1deam0nster/Vending_materials/Img/photo_2022-11-06_20-43-48.jpg

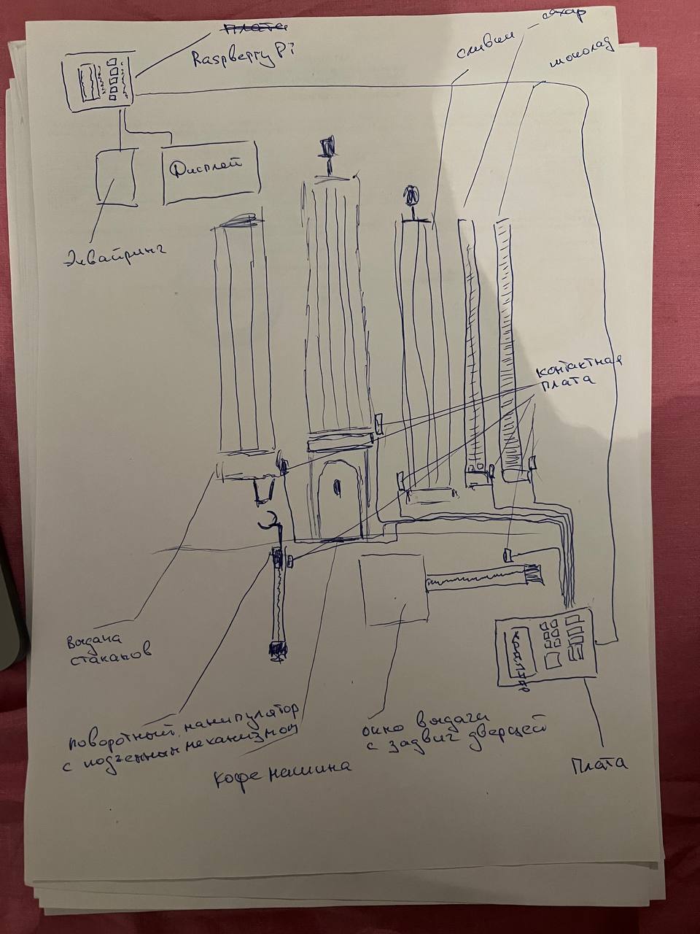
Img/photo_2022-11-06_20-43-48.jpg
