1deam0nster/Vending_materials/Arduino/New firmware arduino/AlmaVending_controll_beta/commands.h

// Открытие и закрытие затвора
void open_mini_servo(){
    //----Открыть затвор
  myservo.attach(turrel_cap_servo_mini);
  for (pos_key = 90; pos_key >= 0; pos_key -= 1) { // goes from 180 degrees to 0 degrees
    myservo.write(pos_key);              // tell servo to go to position in variable 'pos'
    delay(5);                       // waits 15ms for the servo to reach the position
  }
  myservo.detach();
}

void close_mini_servo(){
  //----Закрыть затвор
  myservo.attach(turrel_cap_servo_mini);
  for (pos_key = 0; pos_key <= 90; pos_key += 1) { // goes from 0 degrees to 180 degrees
    // in steps of 1 degree
    myservo.write(pos_key);              // tell servo to go to position in variable 'pos'
    delay(15);                       // waits 15ms for the servo to reach the position
  }
  myservo.detach();
}


//-----------------Проверка-------------
void shake_cap_turrel(){
  //возврат в обычное положение для прокручивания турели
  for (big_pos_cap = 500; big_pos_cap <= 1800; big_pos_cap += 1) {
    cap_drop.writeMicroseconds(big_pos_cap);              
    delay(2);                       
  }
  turrelCurrentPosition = turrel.currentPosition();
  turrel_rotate(turrelCurrentPosition + 50, 1000, 1000);
  delay(100);
  turrel_rotate(turrelCurrentPosition - 50, 1000, 1000);
  delay(100);
  turrel_rotate(turrelCurrentPosition + 50, 1000, 1000);
  delay(100);
  turrel_rotate(turrelCurrentPosition - 50, 1000, 1000);
  for (big_pos_cap = 1800; big_pos_cap >= 1200; big_pos_cap -= 1) {
    cap_drop.writeMicroseconds(big_pos_cap);              
    delay(10);                       
  }
  cap_check();
}

void good_state_drop(){
  Serial.println("начало сброса"); 
  //сброс капсулы
  for (big_pos_cap = 1200; big_pos_cap >= 500; big_pos_cap -= 1) {
    cap_drop.writeMicroseconds(big_pos_cap);              
    delay(5);                       
  }
  
  //возврат в обычное положение
  for (big_pos_cap = 500; big_pos_cap <= 2500; big_pos_cap += 1) {
    cap_drop.writeMicroseconds(big_pos_cap);              
    delay(2);                       
  }
  
  close_mini_servo();

  //положение для прокручивания турели и загрузки капсулы
  for (big_pos_cap = 2500; big_pos_cap >= 1800; big_pos_cap -= 1) {
    cap_drop.writeMicroseconds(big_pos_cap);              
    delay(5);                       
  }
}

void false_state_drop(){
  //возврат в обычное положение
  for (big_pos_cap = 1200; big_pos_cap <= 2500; big_pos_cap += 1) {
    cap_drop.writeMicroseconds(big_pos_cap);              
    delay(2);                       
  }
  
  close_mini_servo();

  //положение для прокручивания турели и загрузки капсулы
  for (big_pos_cap = 2500; big_pos_cap >= 1800; big_pos_cap -= 1) {
    cap_drop.writeMicroseconds(big_pos_cap);              
    delay(5);                       
  }
  Serial.println("Очередь не выпадает");
}

void cap_check(){
  bool check = digitalRead(ir_cap);
  bool check_state;
  DEBUG(cap_check_value);
  cap_check_value += 1;
  switch (check) {
    case 0: 
      check_state = 0;
      Serial.println("Cap OK"); 
      good_state_drop();
      break; 
    case 1: 
      check_state = 1; 
      switch (cap_check_value) {
        case 0: Serial.println("Cap FALSE"); shake_cap_turrel(); break;
        case 1: Serial.println("Cap FALSE"); shake_cap_turrel(); break;
        case 2: Serial.println("Cap FALSE"); shake_cap_turrel(); break;
        case 3: Serial.println("ALL FALSE"); cap_check_value = 0; false_state_drop(); break;
      }
  }
}

// -----------------Command C0-------------
void drop_cap()
{
  //приподнимаем капсулы 
  for (big_pos_cap = 1800; big_pos_cap <= 2500; big_pos_cap += 1) {
    cap_drop.writeMicroseconds(big_pos_cap);              
    delay(5);                       
  }

  //открывваем мини серву
  open_mini_servo();
  
  //положение для загрузки капсулы
  for (big_pos_cap = 2500; big_pos_cap >= 1800; big_pos_cap -= 1) {
    cap_drop.writeMicroseconds(big_pos_cap);              
    delay(5);                       
  }

  Serial.println("забираем капсулу и идем в позицию проверки"); 
  //забираем капсулу и идем в позицию проверки
  for (big_pos_cap = 1800; big_pos_cap >= 1200; big_pos_cap -= 1) {
    cap_drop.writeMicroseconds(big_pos_cap);              
    delay(10);                       
  }

  //код для проверки капсулы
  Serial.println("код для проверки капсулы"); 
  cap_check();
}




// -----------------Command C1-------------
void check_machine() {
  pinMode(cofe_machine_check_button_pin, OUTPUT);
  digitalWrite(cofe_machine_check_button_pin, LOW);
  delay(2000);
  digitalWrite(cofe_machine_check_button_pin, HIGH);
  Serial.println(F("Check machine true"));
  void display_print();
}

// -----------------Command C2-------------
void start_coffe() {
  pinMode(coffe_machine_start_pin, OUTPUT);
  digitalWrite(coffe_machine_start_pin, LOW);
  //delay(1.5 * 60 * 1000); //sleep some minute
  delay(10000);
  do {
    // 1 - можно загружать
    // 0 - наливает кофе
    machine_sensor = digitalRead(cofe_machine_ir);
    Serial.println("Сенсор == 1");
    digitalWrite(coffe_machine_start_pin, LOW);
  } while (machine_sensor == 1);
  delay(7000);
  digitalWrite(coffe_machine_start_pin, HIGH);
  Serial.println(F("End coffe works"));
}
// -----------------Command C4-------------
void choco_check() {
  if (digitalRead(choco_ir_control) == 0) {
    Serial.println("Choco OK");
  } else {
    Serial.println("Choco False");
  }
}

// -----------------Command C5-------------
void sugar_check() {
  if (digitalRead(sugar_ir_control) == 0) {
    Serial.println("Sugar OK");
  } else {
    Serial.println("Sugar False");
  } 
}

// -----------------Command P0-------------
void sugar_command() {
  sugar.attach(sugar_servo);
  delay(1000);
  sugar.write(80);
  delay(1000);
  sugar.write(180);
  delay(1000);
  sugar.write(80);
  sugar.detach();
}
// -----------------Command P1-------------
void chocolate_command() {
  chocolate.attach(choco_servo);
  delay(100);
  chocolate.write(180);
  delay(1000);
  chocolate.write(70);
  delay(1000);
  chocolate.write(180);
  chocolate.detach();
}
