1deam0nster/Vending_materials/Arduino/PlatformIO project/include/turel_y.h

// -----------------Command T2-------------
void rotate_tower2() {
  Serial.println("Turrel X capsule - false");
}

//крутим турель Y до концевика
void homing_turrel2()
{
  long initial_homing = -1;
  turel_Y.enable();
  turel_Y.move(200);
  delay(1000);
  while (digitalRead(turrel_switch_y)) {  // Make the Stepper move CCW until the switch is activated
    turel_Y.move(initial_homing);  // Set the position to move to
    initial_homing++;  // Decrease by 1 for next move if needed
    delay(5);
  }
  initial_homing = 1;
  while (!digitalRead(turrel_switch_y)) { // Make the Stepper move CW until the switch is deactivated
    turel_Y.enable();
    turel_Y.move(turrel_switch_y);  // Set the position to move to
    initial_homing--;  // Decrease by 1 for next move if needed
    delay(5);
  }
//  stepperY.move(-200);
  turel_Y.disable();// DISABLE MOTOR Y
}

//тройная проверка инфракрасного датчика на турели Y
bool ir_cap_check_y() {
  bool check_1 = false;
  bool check_2 = false;
  bool check_3 = false;
  bool check_4 = false;
  bool check_5 = false;
  bool val = false;
  delay(50);
  check_1 = digitalRead(ir_cap_y);
  delay(100);
  check_2 = digitalRead(ir_cap_y);
  delay(100);
  check_3 = digitalRead(ir_cap_y);
  delay(100);
  check_4 = digitalRead(ir_cap_y);
  delay(100);
  check_5 = digitalRead(ir_cap_y);
  delay(50);
  if (check_1 == true | check_2 == true | check_3 == true | check_4 == true | check_5 == true) {
    val = true;
    return (val);
  } else {
    val = false;
    return (val);
  }
}



//преверка есть ли капсула, крутим турель Y
void check_turrelfn2()
{
  bool capsule_state = ir_cap_check_y();

  //---------- 1 проверка-----------
  if (capsule_state == true) {
    //----Открываем вехнюю серву
    servo.attach(10);
    servo.write(0);

    //----Запуск поиска нуля
    homing_turrel2();

    //----Закрываем верхнюю серву
    servo.write(60);
    delay(1000);
    servo.detach();
    delay(1000);

    capsule_state = ir_cap_check_y();
    //----Если приехала пустая ячейка, запускаем еще раз
    //---------- 2 проверка-----------
    if (capsule_state == true) {
      //----Открываем вехнюю серву
      servo.attach(10);
      servo.write(0);

      //----Запуск поиска нуля
      homing_turrel2();

      //----Закрываем верхнюю серву
      servo.write(60);
      delay(1000);
      servo.detach();
    } else {Serial.println("Turrel X capsule - true");}

    capsule_state = ir_cap_check_y();
    //----Если приехала пустая ячейка, пишем что пустая турель
    //---------- 3 проверка-----------
    if (capsule_state == true) {
      //---Пишем в серийный порт что нету капсул в турели
      Serial.println("Turrel Y capsule - false");
    } else {Serial.println("Turrel X capsule - true");}

  } else {
    Serial.println("Turrel Y capsule - true");
  }
}

//--Проверка второй турели
void check_servo_y() {
  //----Проверка на нижнюю серву
  servo.attach(11);
  servo.write(80);
  delay(1000);
  servo.detach();

  //----Проверка на верхнюю серву
  servo.attach(10);
  servo.write(0);
  delay(500);
  servo.write(60);
  delay(1000);
  servo.detach();
}

// -----------------Command C1-------------
void dropcap_y()
{
  //----закрыть нижнюю
  servo.attach(11);
  servo.write(0);
  delay(1000);
  servo.write(80);
  delay(1000);
  servo.detach();

  //----открыть верх
  servo.attach(10);
  servo.write(0);
  delay(1000);
  servo.write(60);
  delay(1000);
  servo.detach();

  //----Проверка капсул в башне
  //check_turrelfn();               -----Из за висяка МК отдельная команда C1
}
