1deam0nster/Vending_materials/Arduino/New firmware arduino/AlmaVending_controll_beta/relay.h

// -----------------Command R0-------------

void relay(double n, double t){
  int rel = n;
  uint32_t del = t;
  uint32_t num_rel;
  
  switch (rel) {
    case 1: num_rel = 14; break;  // выбираем это
    case 2: num_rel = 15; break;
    case 3: num_rel = 52; break;
    case 4: num_rel = 41; break;
    case 5: num_rel = 22; break;
    case 6: num_rel = 25; break;
    case 7: num_rel = 50; break;
    case 8: num_rel = 51; break;
  }

  // if (rel == 1)
  //   {
  //     num_rel = 14;
  //   }
  // else if (rel == 2)
  //   {
  //     num_rel = 15;
  //   }
  // else if (rel == 3)
  //   {
  //     num_rel = 16;
  //   }
  // else if (rel == 4)
  //   {
  //     num_rel = 41;
  //   }
  // else if (rel == 5)
  //   {
  //     num_rel = 31;
  //   }
  // else if (rel == 6)
  //   {
  //     num_rel = 2;
  //   }
  // else if (rel == 7)
  //   {
  //     num_rel = 1;
  //   }
  // else if (rel == 8)
  //   {
  //     num_rel = 0;
  //   }
  
//  Serial.print("relay = ");
//  Serial.println(num_rel);
//  Serial.print("delayRelay = ");
//  Serial.println(del);
//  Serial.println("-------------");
  pinMode(num_rel, OUTPUT);
  digitalWrite(num_rel, LOW);
  delay(del);
  digitalWrite(num_rel, HIGH);

}

void relayfn()
{
  int newNValue = N;
  int newTValue = T;

  if (Commands.availableValue('N')) // ADDED parameter D in S0
  newNValue = Commands.GetValue('N');
  
  if (Commands.availableValue('T')) // ADDED parameter D in S0
  newTValue = Commands.GetValue('T');

//  Serial.print("relay = ");
//  Serial.println(newNValue);
//  Serial.print("delayRelay = ");
//  Serial.println(newTValue);
//  Serial.println("-------------");
  
  relay(newNValue, newTValue);
  
}
