1deam0nster/Vending_materials/Python/Stuff/other/2.py

import threading
import serial

port = '/dev/ttyS0'
baud = 9600

serial_port = serial.Serial(port, baud, timeout=0)

def handle_data(data):
    print(data)

def read_from_port(ser):
    while True:
       reading = ser.readline().decode("utf-8")
       handle_data(reading)

thread = threading.Thread(target=read_from_port, args=(serial_port,))
thread.start()
